sebastian-stumpf/swepp/pcb/sepp/models/fpc-connector-breakout.step

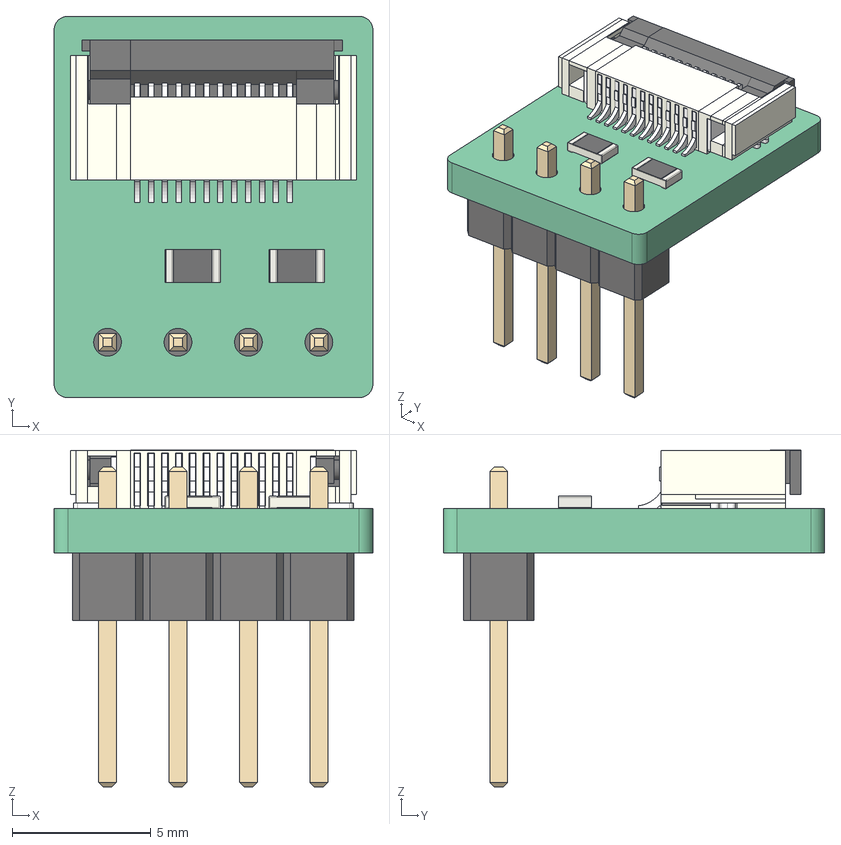
[picture p17: CAD file, 2023-11-14]
pcb/sepp/models/fpc-connector-breakout.step
11.5 x 13.8 x 12.1 mm
Pcb_5954
R1_R_0805_2012Metric_676ca8c0b9b2
J1_PinHeader_1x04_P254mm_Vertical_3e6cda006090
R2_R_0805_2012Metric_2709119373ce
FPC-12
FPC-013
FPC-014
FPC-015
FPC-016
FPC-017
FPC-018
FPC-019
FPC-020
FPC-021
FPC-022
FPC-023
FPC-024
FPC-025
FPC-026
FPC-027
FPC-028
