sebastian-stumpf/swepp/pcb/sepp/models/tact-switch.step

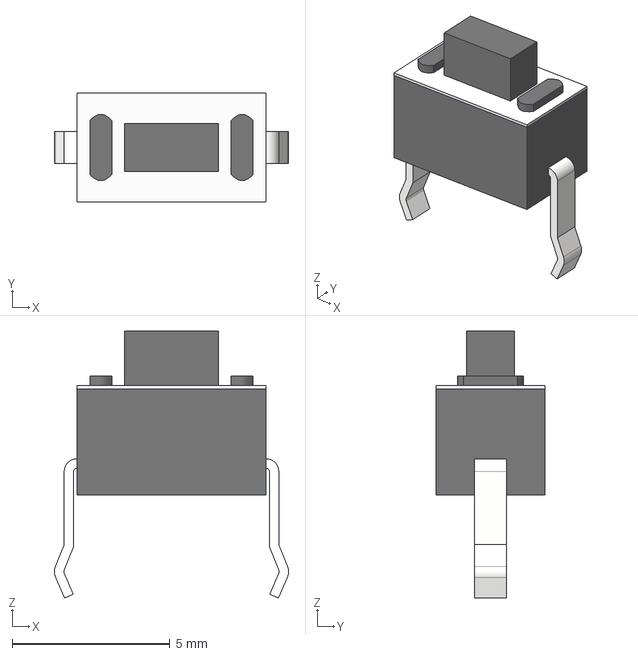
[picture p18: CAD file, 2023-11-14]
pcb/sepp/models/tact-switch.step
7.42 x 3.46 x 8.46 mm
