sebastian-stumpf/swepp/pcb/sepp/models/pg1350-mbk.step

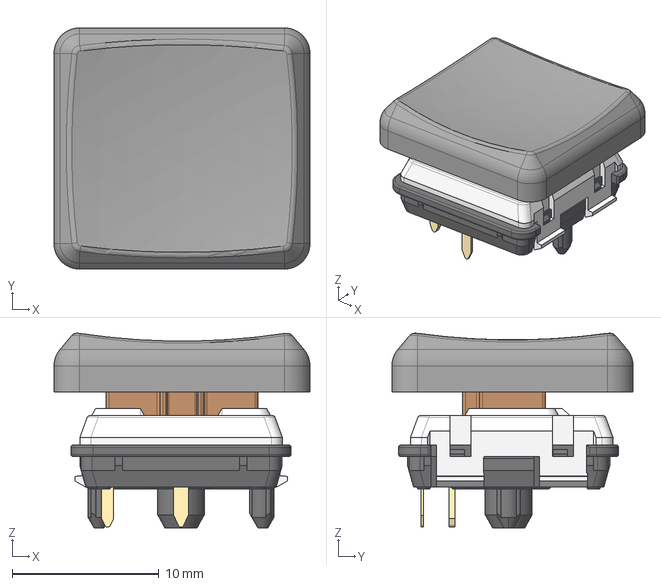
[picture p19: CAD file, 2023-11-14]
pcb/sepp/models/pg1350-mbk.step
17.4 x 16.4 x 13.3 mm
(Unsaved)
Document x 5
