sebastian-stumpf/swepp/pcb/sepp/models/EC12E-085.step

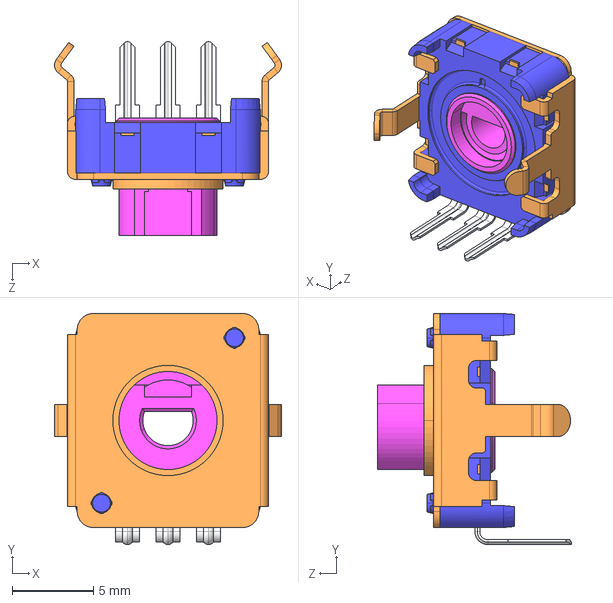
[picture p20: CAD file, 2023-11-14]
pcb/sepp/models/EC12E-085.step
14.0 x 14.3 x 11.9 mm
