sebastian-stumpf/swepp/pcb/sepp/models/SKRTLAE010.step

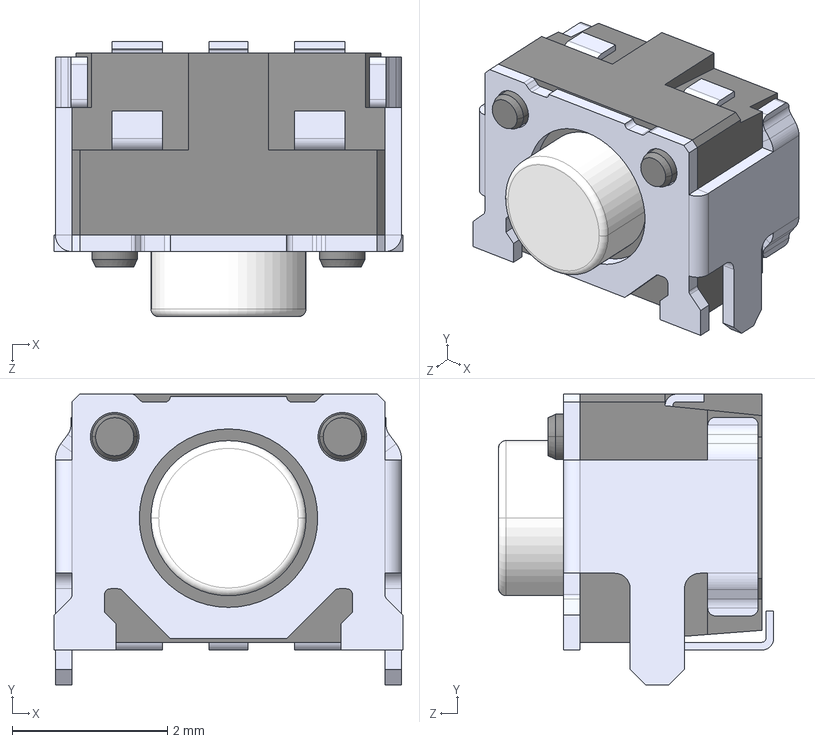
[picture p21: CAD file, 2023-11-14]
pcb/sepp/models/SKRTLAE010.step
4.50 x 3.75 x 3.55 mm
