sebastian-stumpf/swepp/pcb/sepp/models/SW_SKHLLC.step

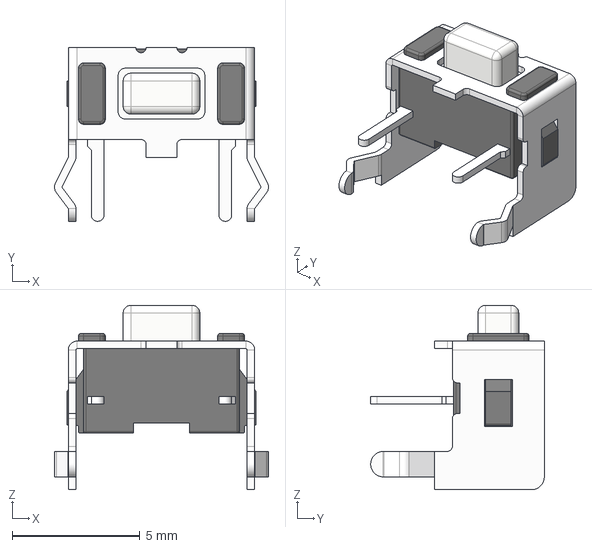
[picture p22: CAD file, 2023-11-14]
pcb/sepp/models/SW_SKHLLC.step
8.38 x 6.80 x 7.22 mm
