sebastian-stumpf/swepp/pcb/sepp/models/LED_SK6812MINI-E.step

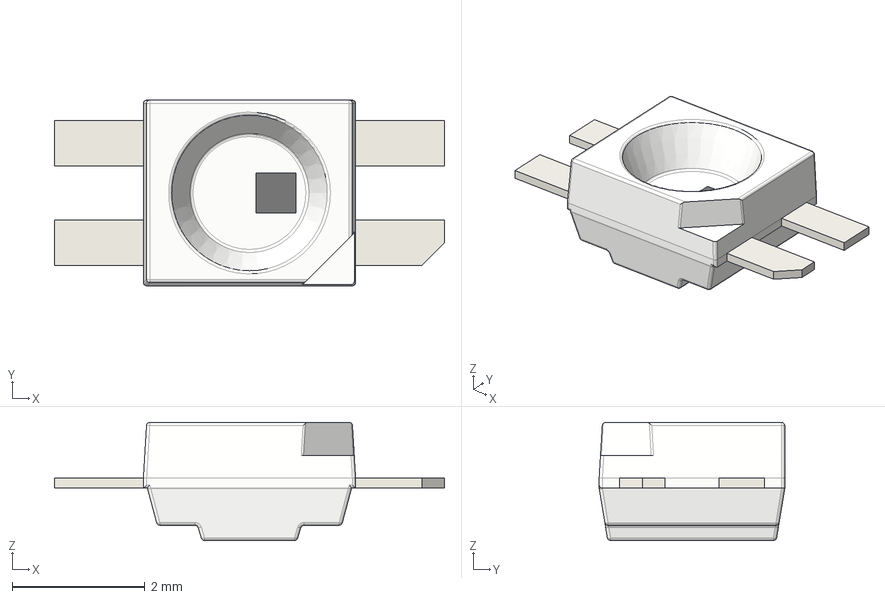
[picture p24: CAD file, 2023-11-14]
pcb/sepp/models/LED_SK6812MINI-E.step
5.88 x 2.80 x 1.78 mm
