sebastian-stumpf/swepp/pcb/sepp/models/SW_PUSH_6mm.step

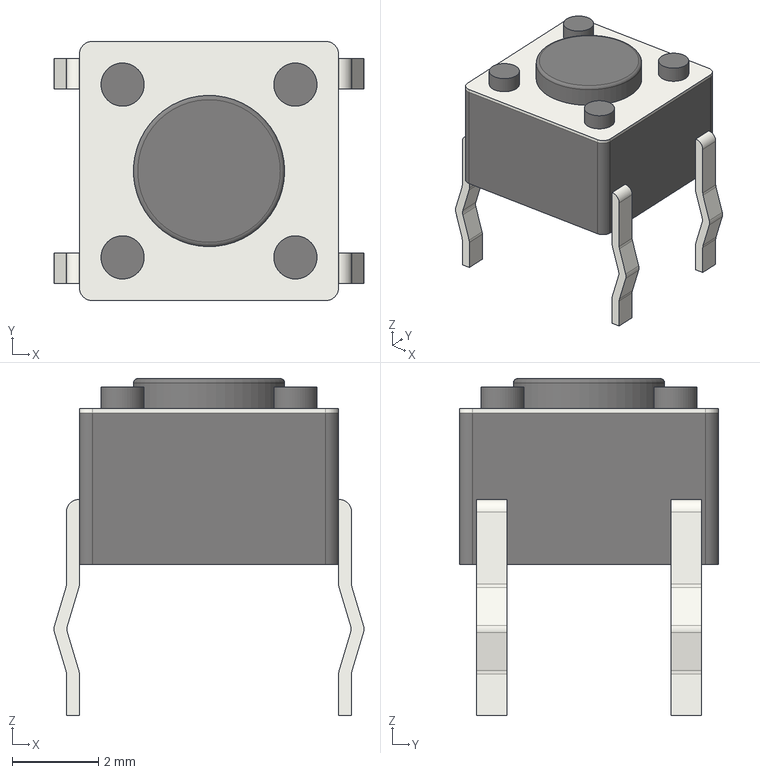
[picture p25: CAD file, 2023-11-14]
pcb/sepp/models/SW_PUSH_6mm.step
7.17 x 6.00 x 7.80 mm
