sebastian-stumpf/swepp/pcb/sepp/models/mx_kecap.step

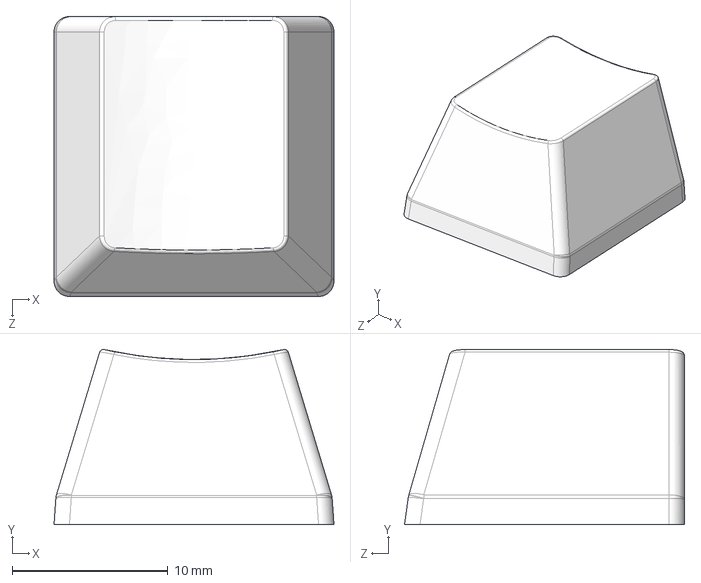
[picture p27: CAD file, 2023-11-14]
pcb/sepp/models/mx_kecap.step
18.0 x 11.3 x 18.0 mm
