sebastian-stumpf/swepp/pcb/sepp/models/abomination-trackpad-holder.step

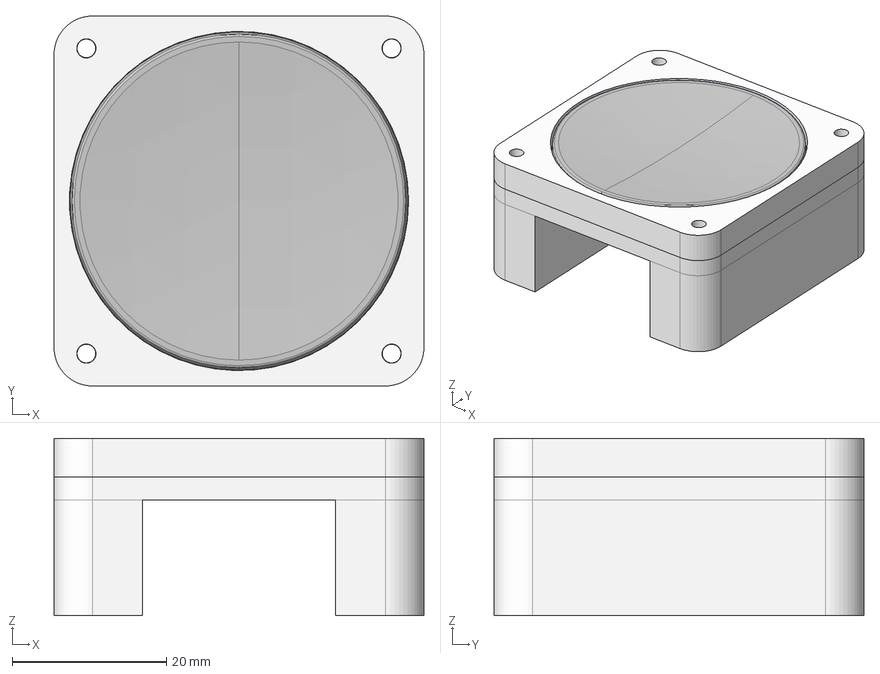
[picture p28: CAD file, 2023-11-14]
pcb/sepp/models/abomination-trackpad-holder.step
48.0 x 48.0 x 23.0 mm
trackpad
top
bottom
